ISS-Lab-Unibo/Agro_LoRaInductiveFruitGauge/Configuring software/python files/risorse.py

# Resource object code (Python 3)
# Created by: object code
# Created by: The Resource Compiler for Qt version 6.11.1
# WARNING! All changes made in this file will be lost!

# from PySide6 import QtCore <-- replace this line
from PyQt6 import QtCore

qt_resource_data = b"\
\x00\x00\x03\x09\
\x89\
PNG\x0d\x0a\x1a\x0a\x00\x00\x00\x0dIHDR\x00\
\x00\x00\x14\x00\x00\x00\x13\x08\x03\x00\x00\x00\xa7R\xdd\x87\
\x00\x00\x00 cHRM\x00\x00z&\x00\x00\x80\x84\
\x00\x00\xfa\x00\x00\x00\x80\xe8\x00\x00u0\x00\x00\xea`\
\x00\x00:\x98\x00\x00\x17p\x9c\xbaQ<\x00\x00\x00\xfc\
PLTE\xff\xff\xff\xff\xfc\xfc\xfb\xd0\xd1\xf4sx\
\xef;B\xed '\xed\x1b#\xee,3\xf1MT\xf7\
\x98\x9c\xfe\xf2\xf2\xff\xfd\xfd\xff\xfe\xfe\xfe\xf1\xf2\xf3l\
q\xec\x10\x18\xed\x17\x1f\xed\x1c$\xed\x19!\xec\x14\x1c\
\xef07\xf8\xa4\xa7\xfc\xda\xdb\xef3:\xec\x09\x12\xed\
\x1f'\xed\x1d%\xed\x1e&\xed\x16\x1f\xeb\x09\x11\xf4q\
v\xfe\xef\xf0\xee/6\xed\x22)\xed!)\xeb\x05\x0e\
\xf5}\x81\xf3bg\xec\x0b\x14\xed (\xec\x0d\x16\xfa\
\xbb\xbd\xfa\xc3\xc5\xec\x12\x1a\xf0GN\xf2_e\xec\x11\
\x1a\xed\x1f&\xec\x13\x1b\xfb\xca\xcc\xee&.\xed\x1a\x22\
\xec\x0a\x13\xf6\x8f\x93\xec\x0d\x15\xf3jo\xec\x0e\x17\xf2\
^d\xec\x13\x1c\xf0AH\xf2`e\xec\x0e\x16\xf9\xb6\
\xb9\xfd\xeb\xec\xee+2\xec\x11\x19\xeb\x06\x0f\xf4x}\
\xfc\xd6\xd8\xee.6\xed\x18 \xeb\x08\x11\xf3mr\xfe\
\xee\xef\xf3hn\xec\x0f\x18\xee*1\xf8\xa2\xa6\xfb\xce\
\xd0\xef;A\xee(0\xf1NU\xf7\x96\x99\xfd\xea\xeb\
d\x8d\xe8\x0a\x00\x00\x00\x01bKGD\x00\x88\x05\x1d\
H\x00\x00\x00\x09pHYs\x00\x00\x0e\xc3\x00\x00\x0e\
\xc3\x01\xc7o\xa8d\x00\x00\x00\x07tIME\x07\xea\
\x02\x08\x10%#\x92\xcd\xeb.\x00\x00\x00\xd1IDA\
T\x18\xd3u\x90i[\x01Q\x18\x86\x9fA#K\xc6\
K\xe1\x9c\xa3d,\x93%\xdb(\xca.E\x12\xc9\xff\
\xff/\xcd1\x91\xa9<\x1f\xef\xeb]o\x00\x0a\xe0r\
{NT\xef\xa9\xcf\x8f@\x102\x0a\xceB\xaa\x16V\
)\x12\xd5\xce/\x80\xe0\x96\xc5\xe2\x09b\x9c\x88\x0b\x96\
\xbc\xbc\xb2i\xeaZK\xd3w\x84\x9e\xc9\xcaq\xc8\xe5\
u\xfa\x89qS\xb0h1)\x0e\x18\xb1R\xd9\xea\xbf\
\xadT\x0f!\x89Z\x1dh\x98\x0eFF\xf3\x0eP\x9d\
\x8c\xd8}\x0b\xe0\xbfa\xfb\xe1H\xe5\xbf3\xffl\x7f\
\xb4\xb6\x17\xc3\x8e;\xab\xb5\x8e\x14\xd2u~\xd4\xeb\xcb\
?\x07\xc3\xd1\x9er}\xfc$\x99\x82\xc9s\x93KK\
$\xd8\xcbt\xb6s\xf7:7\xa5O3\xfa\xb6x\xb7\
\xd9\xd6\xfc\xd2\xbd2\xcc\x8f\xf5\xe7\xc66\xff\x05\x99\xa0\
 )\xebH\x99\xc8\x00\x00\x00%tEXtda\
te:create\x002026-0\
2-08T16:37:22+00\
:00\xea\xa4\xf0K\x00\x00\x00%tEXtd\
ate:modify\x002026-\
02-08T16:37:22+0\
0:00\x9b\xf9H\xf7\x00\x00\x00(tEXt\
date:timestamp\x002\
026-02-08T16:37:\
35+00:00\xc5\xe1W8\x00\x00\x00\x00\
IEND\xaeB`\x82\
\x00\x00\x03\x11\
\x89\
PNG\x0d\x0a\x1a\x0a\x00\x00\x00\x0dIHDR\x00\
\x00\x00\x14\x00\x00\x00\x13\x08\x03\x00\x00\x00\xa7R\xdd\x87\
\x00\x00\x00 cHRM\x00\x00z&\x00\x00\x80\x84\
\x00\x00\xfa\x00\x00\x00\x80\xe8\x00\x00u0\x00\x00\xea`\
\x00\x00:\x98\x00\x00\x17p\x9c\xbaQ<\x00\x00\x01\x02\
PLTE\xff\xff\xff\xfc\xfe\xfc\xd1\xef\xdav\xcf\x90\
@\xbcd%\xb2O!\xb1K1\xb6XR\xc2s\x9b\
\xdc\xae\xf2\xfa\xf4\xfd\xfe\xfd\xfe\xff\xfep\xcc\x8b!\xb1\
L\x16\xadB\x1d\xafH\x22\xb1L\x1f\xb0J\x1a\xaeE\
5\xb8\x5c\xa6\xe0\xb7\xdb\xf2\xe18\xb9^\x10\xab=%\
\xb2N#\xb1M#\xb1L$\xb2M\x0f\xaa=u\xce\
\x8f\xf0\xfa\xf34\xb7['\xb3P\x0c\xa9:\x80\xd2\x98\
\xfc\xfe\xfdf\xc9\x83\x12\xab?&\xb2O\x14\xac@\xbc\
\xe7\xc9\xc5\xea\xd0\x18\xaeDL\xc0nc\xc8\x81\x18\xad\
D$\xb2N\x19\xaeE\xcb\xed\xd5,\xb4T \xb0K\
\x11\xab>\x92\xd9\xa7\x13\xac@n\xcc\x89\x15\xacAb\
\xc8\x80\x17\xadCF\xbejd\xc8\x81\x14\xacA\xb8\xe6\
\xc6\xec\xf8\xef0\xb6X\x0d\xa9;|\xd1\x95\xd7\xf1\xdf\
\x10\xab>\x1e\xb0I\x0f\xaa<q\xcd\x8c\xef\xf9\xf2l\
\xcb\x88 \xb0J\x16\xadC\x1a\xaeF/\xb6W\xa5\xdf\
\xb6\xd0\xee\xd9w\xcf\x91.\xb5VS\xc2t\x98\xdb\xac\
\xeb\xf8\xee\xfd\xfe\xfe\x83\xff\x0b\xe3\x00\x00\x00\x01bK\
GD\x00\x88\x05\x1dH\x00\x00\x00\x09pHYs\x00\
\x00\x0e\xc3\x00\x00\x0e\xc3\x01\xc7o\xa8d\x00\x00\x00\x07\
tIME\x07\xea\x02\x08\x10%#\x92\xcd\xeb.\x00\
\x00\x00\xd3IDAT\x18\xd3u\xd0yw\xc1@\x14\
\x05\xf0\x1b\xfb\x9e<E%R\x15E,\xb5\xd4\xbe\x14\
mi\xa9\x9d\xd6\xf7\xff*flG\x1c\xee\x9f\xbf3\
of\xde\x05 \x00&\xb3\xc5j\xb3;\x9c.\xb8=\
\xe0\x11\xe0\xf2\xfaD\xc9G\xfe\x071\x10\x04<{\x0b\
=\x86IV\x88\x22\xaa,=E\x0f\xfa\x1c\x135:\
F\xd5\xe2/H0L\xa6\xce\xc6\xa2\xa73l8+\
\xa9\x17Fr\xee\x95\xcd\xe7\x0b\xc5K\xa4b\xe9\x0d(\
W\x0cFz\xb5\x06\xd8\x8cFr\xbd\x01(\xd7\xd8l\
\xdd9y\xf3\xce|\xfb\xc6\xeb\xd7\xff,ux!\xef\
\xc6\x8d\xba=^[\xff\xa3}VE\xfb\xfc\xe2\xbb\x0b\
\x18\xc4\x86\x0ao\x89T\xeb\xf7\xcf\xe8\xd4\xdd\xf8w2\
e}Nf\xe2|q\xb0}\xf3\xcb\x95E\xaf\xac7\
\x7f\xff\xd8r\xdb\x01\xdcz!\x00%\xdc\xa5}\x00\x00\
\x00%tEXtdate:creat\
e\x002026-02-08T16:\
37:22+00:00\xea\xa4\xf0K\x00\
\x00\x00%tEXtdate:modi\
fy\x002026-02-08T16\
:37:22+00:00\x9b\xf9H\xf7\
\x00\x00\x00(tEXtdate:tim\
estamp\x002026-02-0\
8T16:37:35+00:00\
\xc5\xe1W8\x00\x00\x00\x00IEND\xaeB`\x82\
\
"

qt_resource_name = b"\
\x00\x0f\
\x0f\x91\xfe\xe5\
\x00i\
\x00m\x00m\x00a\x00g\x00i\x00n\x00i\x00B\x00o\x00t\x00t\x00o\x00n\x00e\
\x00\x03\
\x00\x00p7\
\x00i\
\x00m\x00g\
\x00\x07\
\x08\xb7W\xa7\
\x00r\
\x00e\x00d\x00.\x00p\x00n\x00g\
\x00\x09\
\x0b\xc1\x8aG\
\x00g\
\x00r\x00e\x00e\x00n\x00.\x00p\x00n\x00g\
"

qt_resource_struct = b"\
\x00\x00\x00\x00\x00\x02\x00\x00\x00\x01\x00\x00\x00\x01\
\x00\x00\x00\x00\x00\x00\x00\x00\
\x00\x00\x00\x00\x00\x02\x00\x00\x00\x01\x00\x00\x00\x02\
\x00\x00\x00\x00\x00\x00\x00\x00\
\x00\x00\x00$\x00\x02\x00\x00\x00\x02\x00\x00\x00\x03\
\x00\x00\x00\x00\x00\x00\x00\x00\
\x00\x00\x000\x00\x00\x00\x00\x00\x01\x00\x00\x00\x00\
\x00\x00\x01\x9c>\x1d\xa0\x98\
\x00\x00\x00D\x00\x00\x00\x00\x00\x01\x00\x00\x03\x0d\
\x00\x00\x01\x9c>\x1d\xa0\x98\
"

def qInitResources():
    QtCore.qRegisterResourceData(0x03, qt_resource_struct, qt_resource_name, qt_resource_data)

def qCleanupResources():
    QtCore.qUnregisterResourceData(0x03, qt_resource_struct, qt_resource_name, qt_resource_data)

qInitResources()
